mfkiwl/arise-ice40up5k/altium/3D models/User Library-LS8.STEP

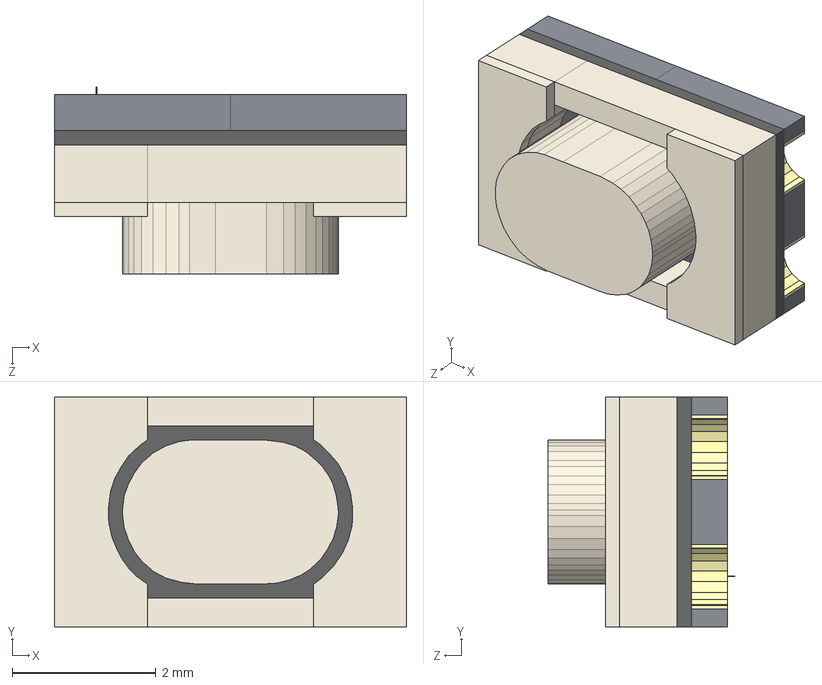
[picture p16: CAD file, 2020-11-03]
altium/3D models/User Library-LS8.STEP
4.90 x 3.20 x 2.61 mm
User Library-LS8_Board_1
User Library-LS8_Extruded_9
User Library-LS8_Extruded_10
User Library-LS8_Extruded_11
User Library-LS8_Extruded_12
User Library-LS8_Extruded_13
User Library-LS8_Extruded_14
User Library-LS8_Extruded_15
User Library-LS8_Extruded_16 x 2
User Library-LS8_Extruded_17 x 2
