mfkiwl/arise-ice40up5k/altium/3D models/User Library-SMD CAPACITOR0402.STEP

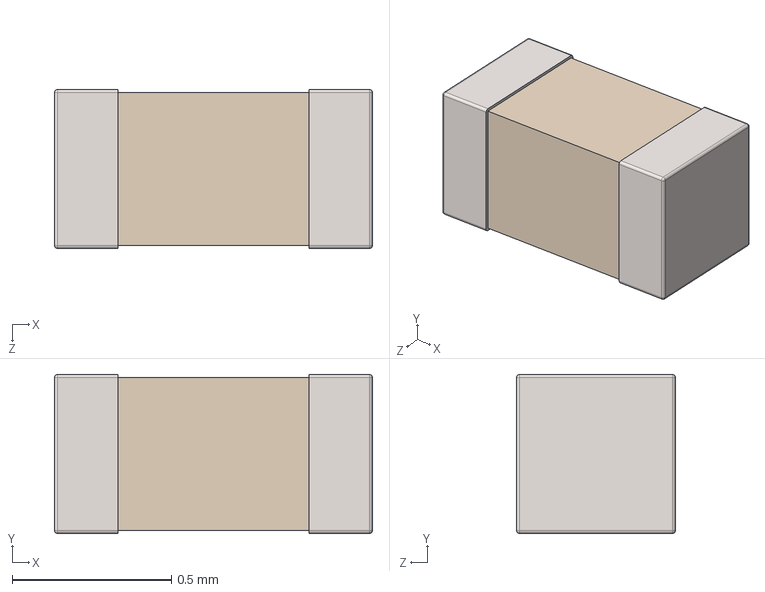
[picture p17: CAD file, 2020-11-03]
altium/3D models/User Library-SMD CAPACITOR0402.STEP
1.00 x 0.5 x 0.5 mm
