mfkiwl/arise-ice40up5k/altium/3D models/User Library-Oscillator2520-4pol.STEP

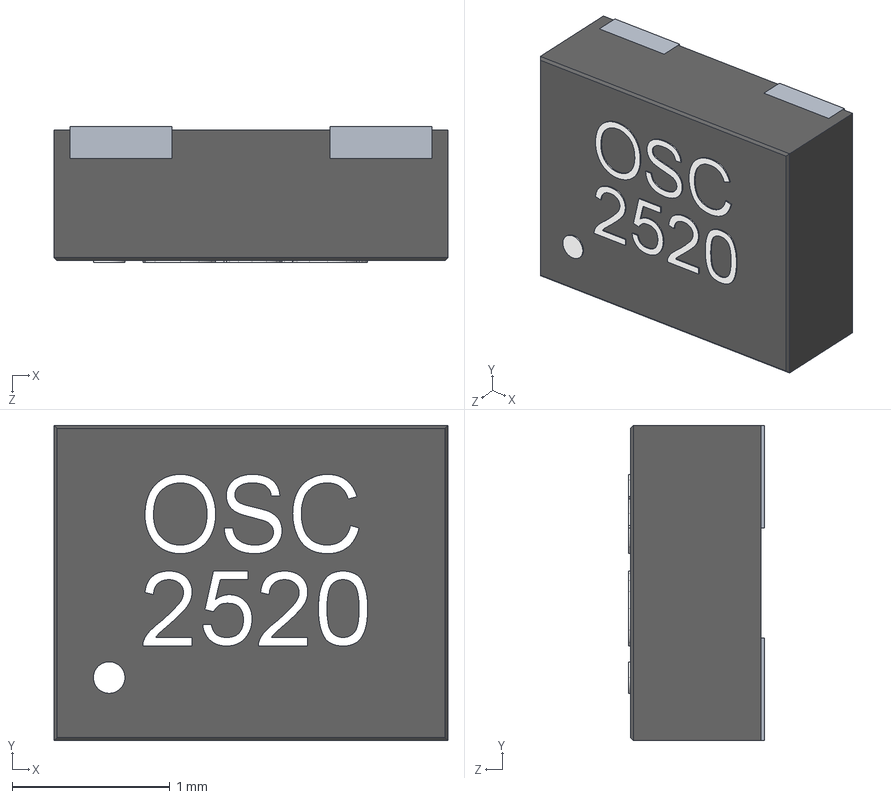
[picture p18: CAD file, 2020-11-03]
altium/3D models/User Library-Oscillator2520-4pol.STEP
2.50 x 2.00 x 0.86 mm
User Library-Oscillator2520-4pol_Pad002
User Library-Oscillator2520-4pol_Pad001
User Library-Oscillator2520-4pol_Cut004
User Library-Oscillator2520-4pol_Zylinder
User Library-Oscillator2520-4pol_Cut
